SAR-mango/Universal-Laser-Driver/spice_sim/ULD_Sim.asc

C1: cap; 22n
C2: cap; 22n
C3: cap; 22µ
C4: cap; 4.7µ
C5: cap; 22µ
D1: diode
D2: diode
D3: diode
D4: diode
L1: ind; 6.8µ
R1: res; 10k
R2: res; 1
R3: res; 10k
R4: res; 300
U1: LTC3129
U2: AD8515
V1: voltage; 3; Rser=100m
Named nets: 0, VIN
.tran 100m startup
